74ls00/HVProgUSB/adapters/AdapterDIP8M16/AdapterDIP8M16.pl0.png

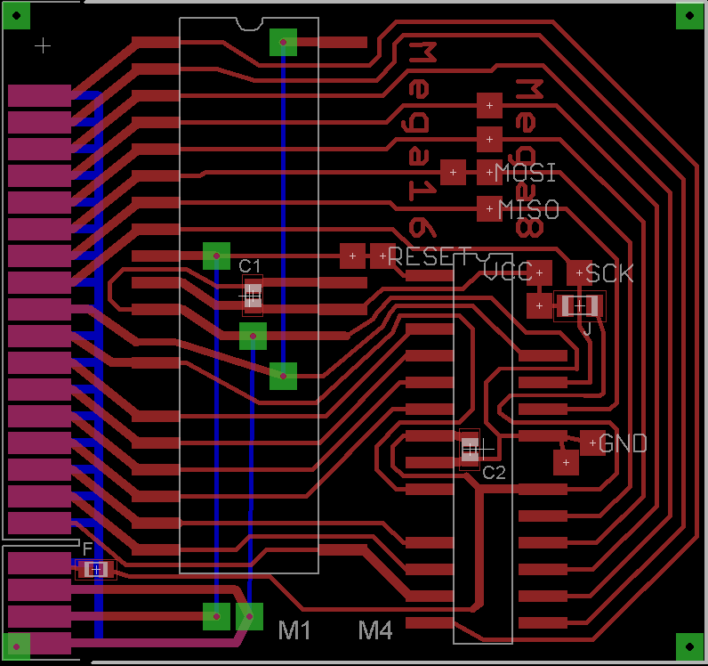
adapters/AdapterDIP8M16/AdapterDIP8M16.pl0.png
