74ls00/HVProgUSB/adapters/AdapterDIP8M16/AdapterDIP.sh.png

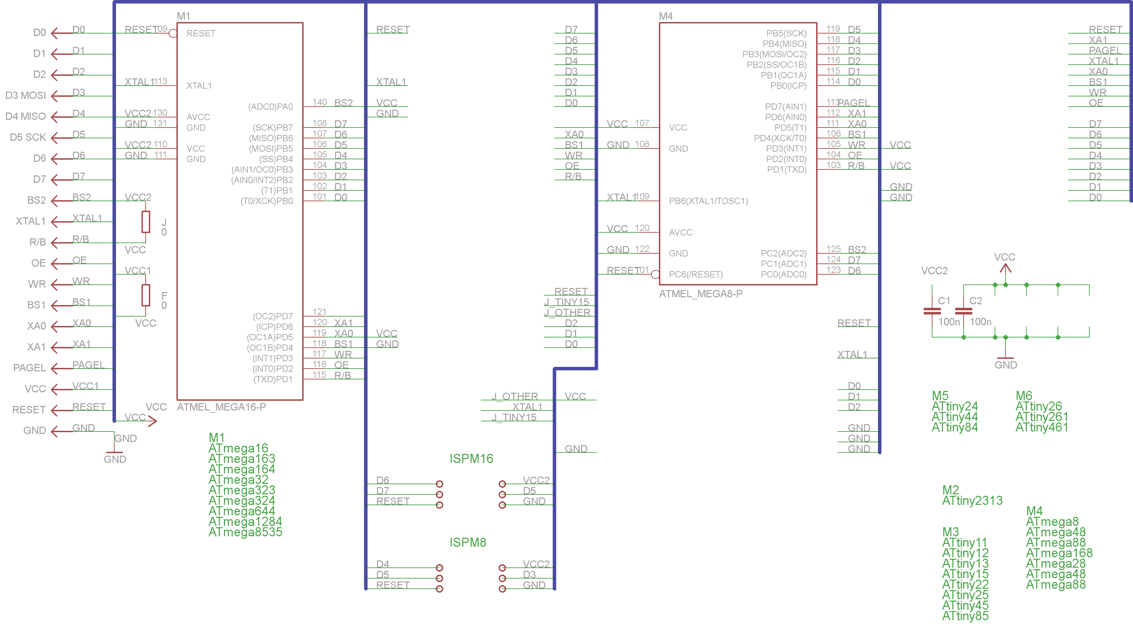
adapters/AdapterDIP8M16/AdapterDIP.sh.png
