74ls00/HVProgUSB/adapters/Leonardo32u4HVPP/100.png

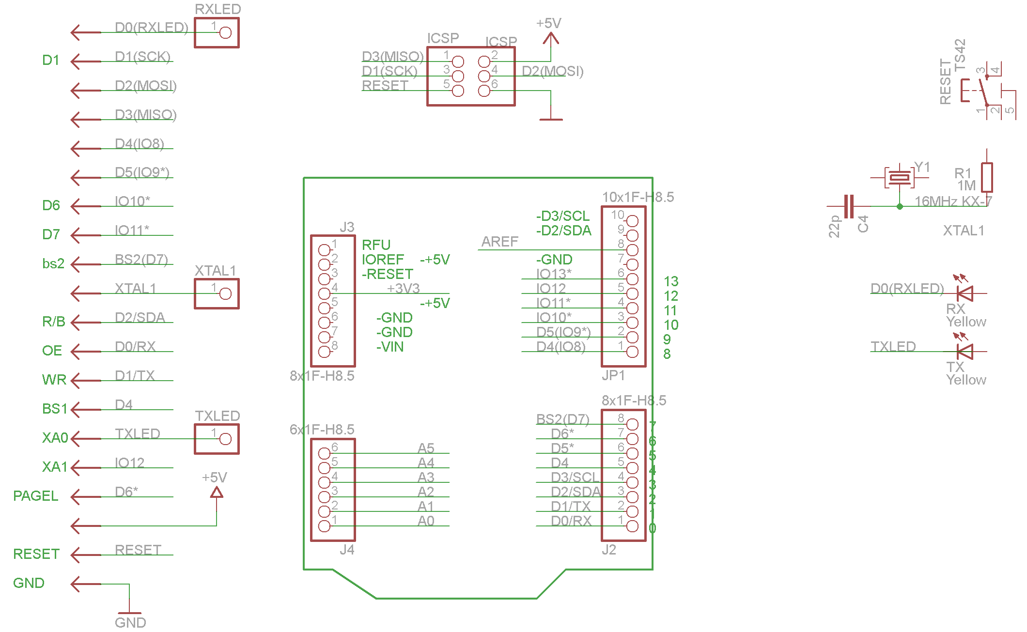
adapters/Leonardo32u4HVPP/100.png
