74ls00/HVProgUSB/adapters/Leonardo32u4HVPP/200.png

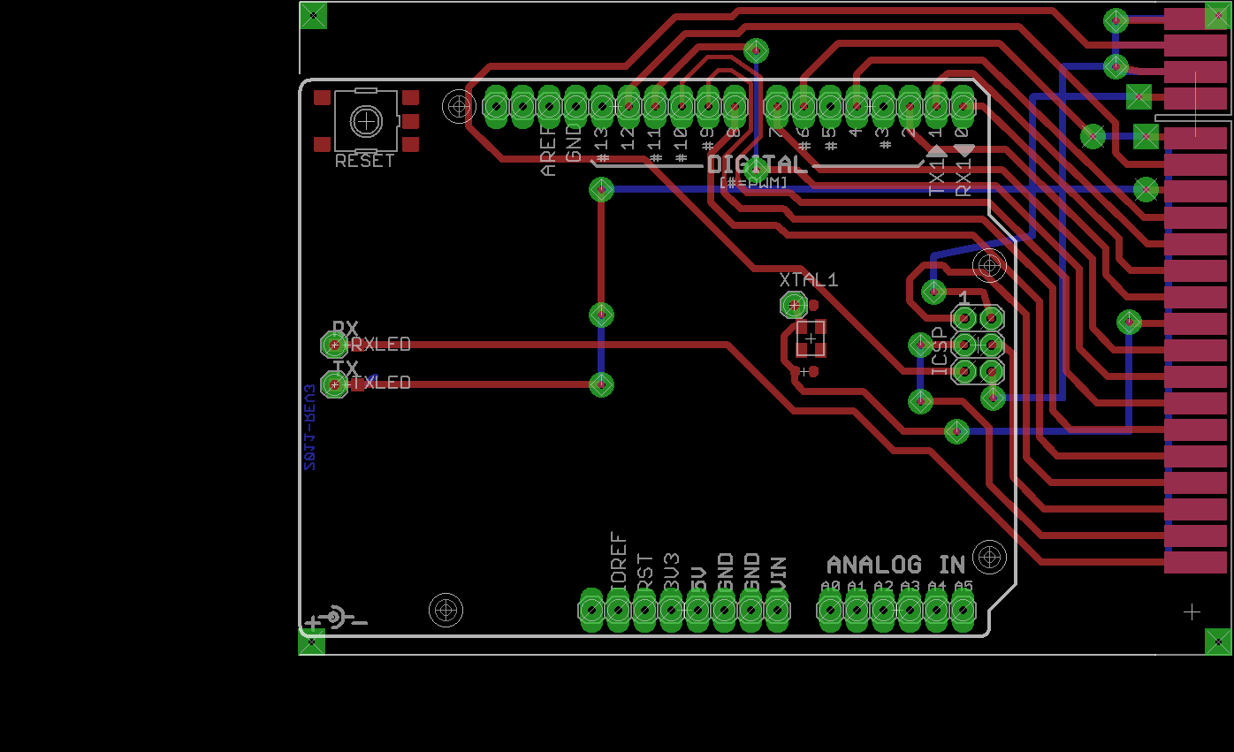
adapters/Leonardo32u4HVPP/200.png
