74ls00/HVProgUSB/adapters/leonardo32u4hvpp/hvpp32u4.png

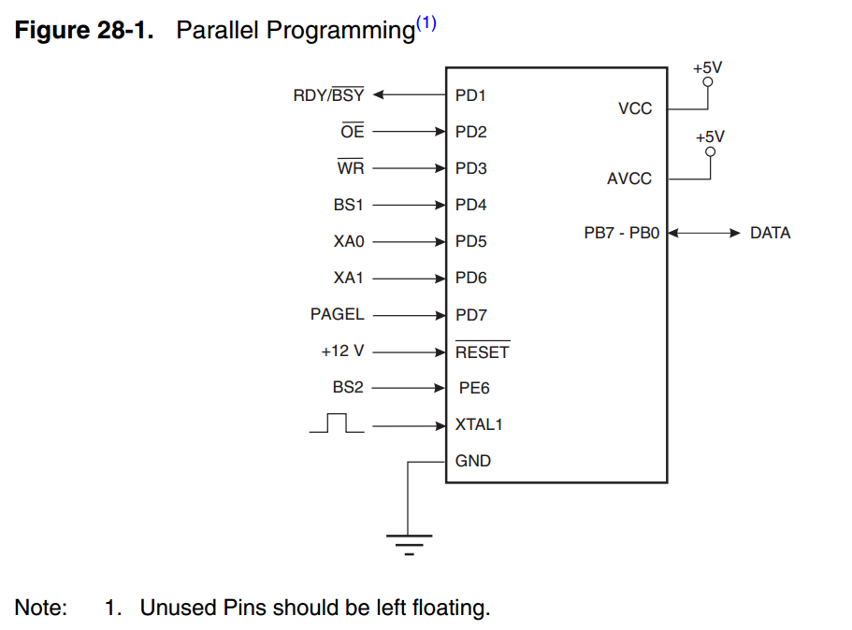
adapters/leonardo32u4hvpp/hvpp32u4.png
