74ls00/HVProgUSB/adapters/ZIF_QFP32/pcb.png

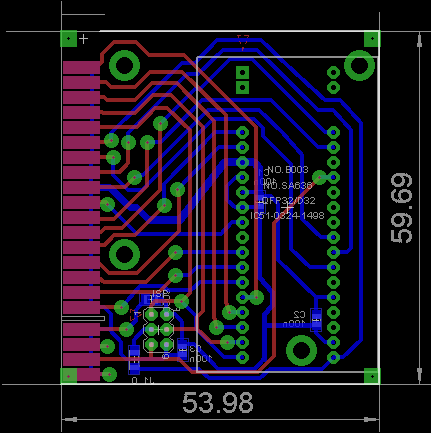
adapters/ZIF_QFP32/pcb.png
