74ls00/HVProgUSB/adapters/ZIF_QFP32/sch.png

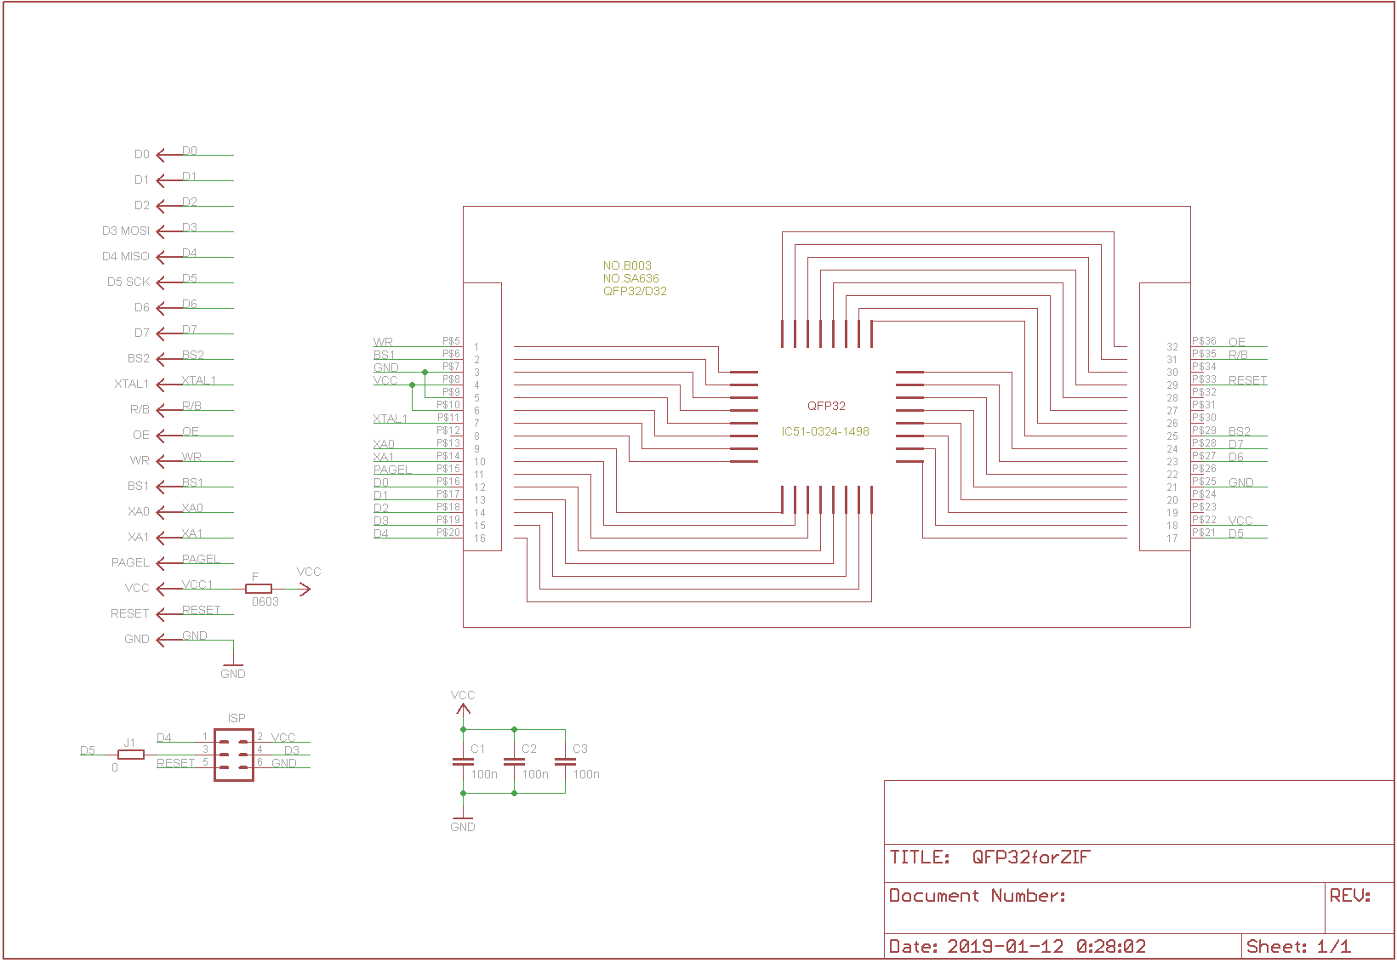
adapters/ZIF_QFP32/sch.png
