74ls00/HVProgUSB/doc/images/jisp8535.png

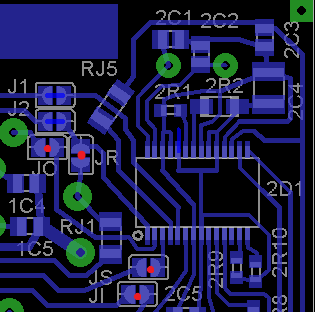
doc/images/jisp8535.png
