74ls00/HVProgUSB/pic/DSC01173.JPG

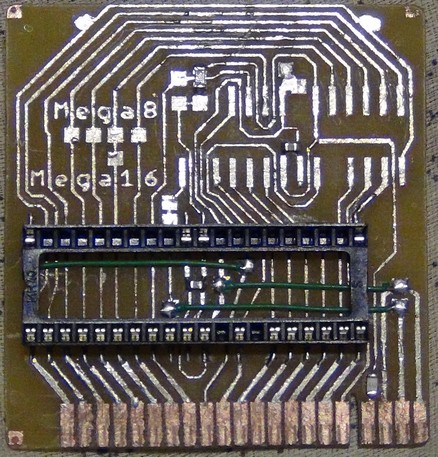
pic/DSC01173.JPG
