74ls00/HVProgUSB/pic/DSC01176.png

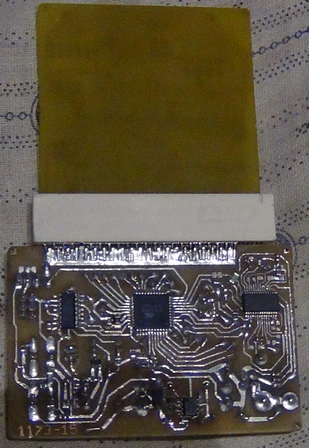
pic/DSC01176.png
