74ls00/HVProgUSB/programmer/3d/HWProgUSB.3d.png

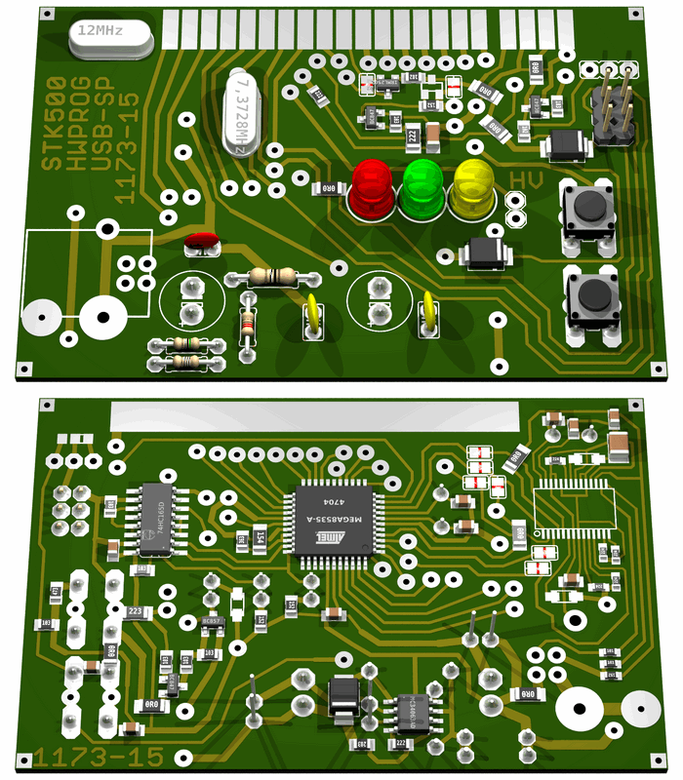
programmer/3d/HWProgUSB.3d.png
