74ls00/HVProgUSB/sprint/Sl_import.png

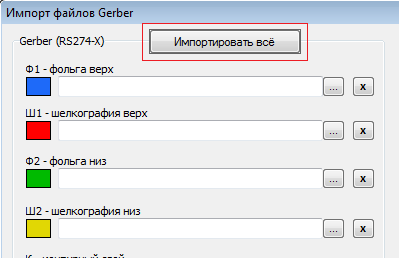
sprint/Sl_import.png
