74ls00/HVProgUSB/sprint/SL_print.png

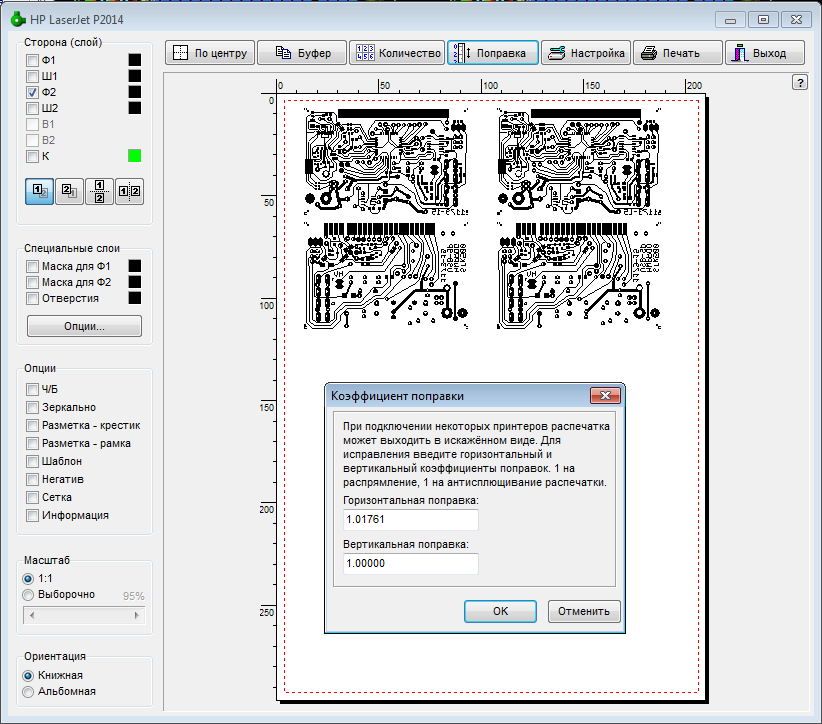
sprint/SL_print.png
